brewer-michael/ns-cspgasp-rebuild/ref-images/IMG_2893.jpg

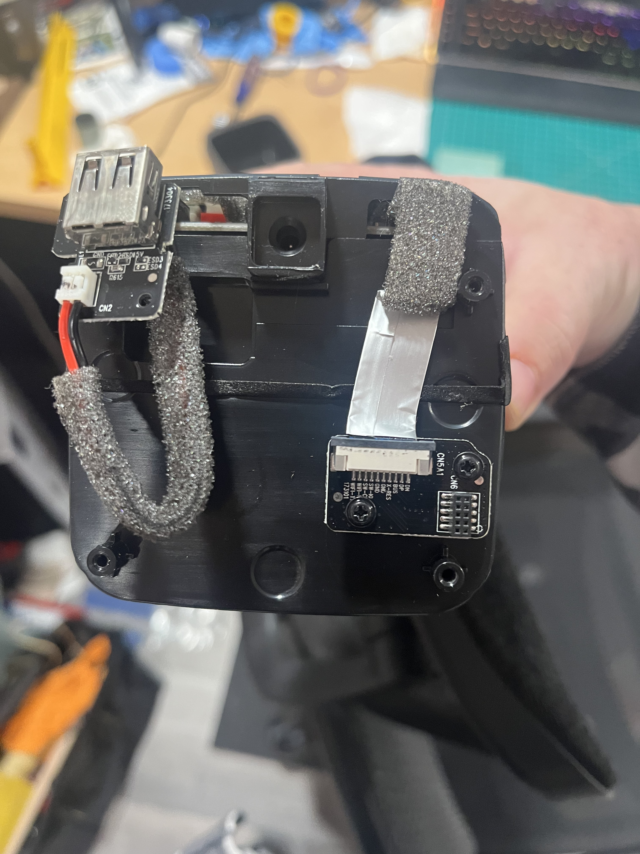
ref-images/IMG_2893.jpg
