brewer-michael/ns-cspgasp-rebuild/ref-images/IMG_2894.jpg

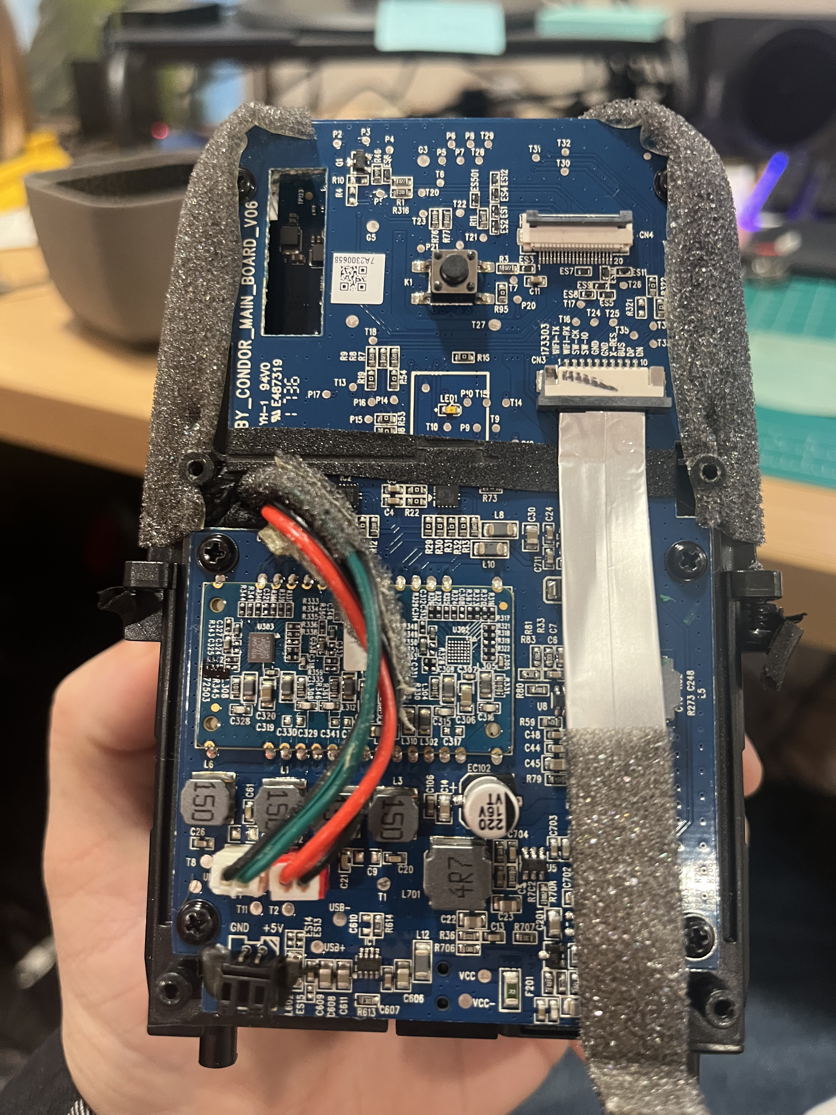
ref-images/IMG_2894.jpg
