brewer-michael/ns-cspgasp-rebuild/ref-images/IMG_2895.jpg

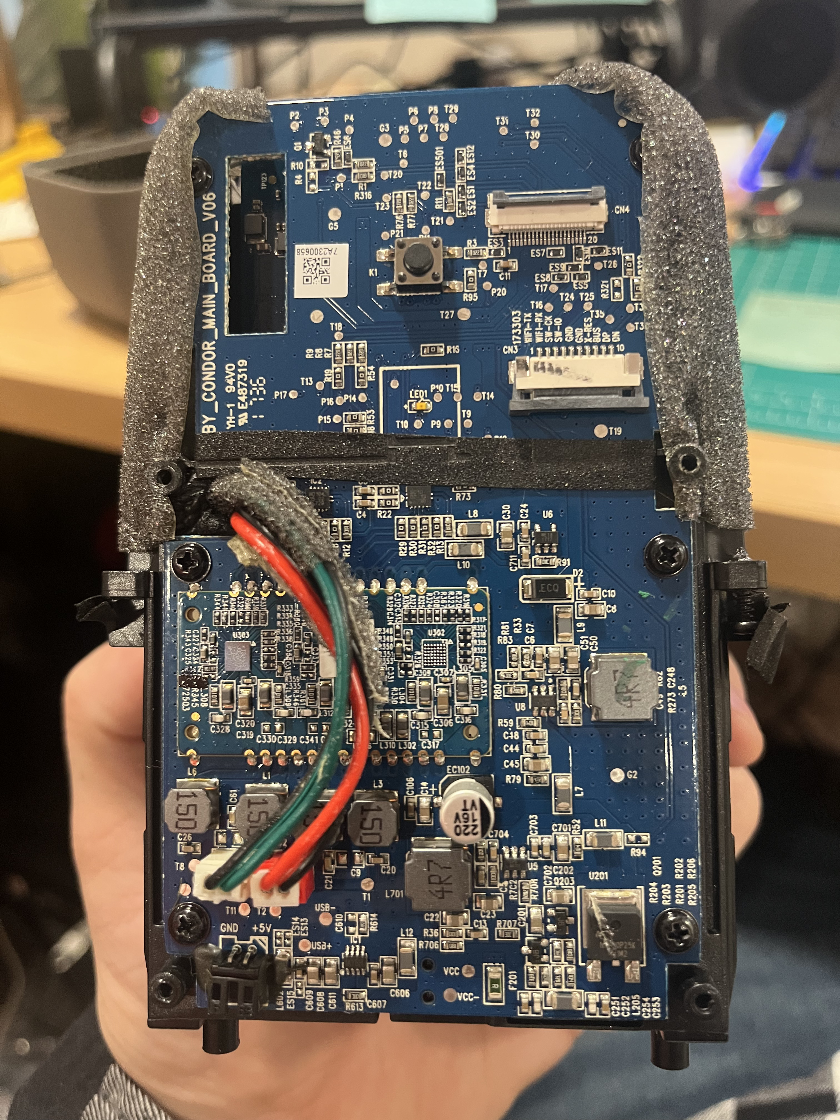
ref-images/IMG_2895.jpg
