brewer-michael/ns-cspgasp-rebuild/ref-images/IMG_2897.jpg

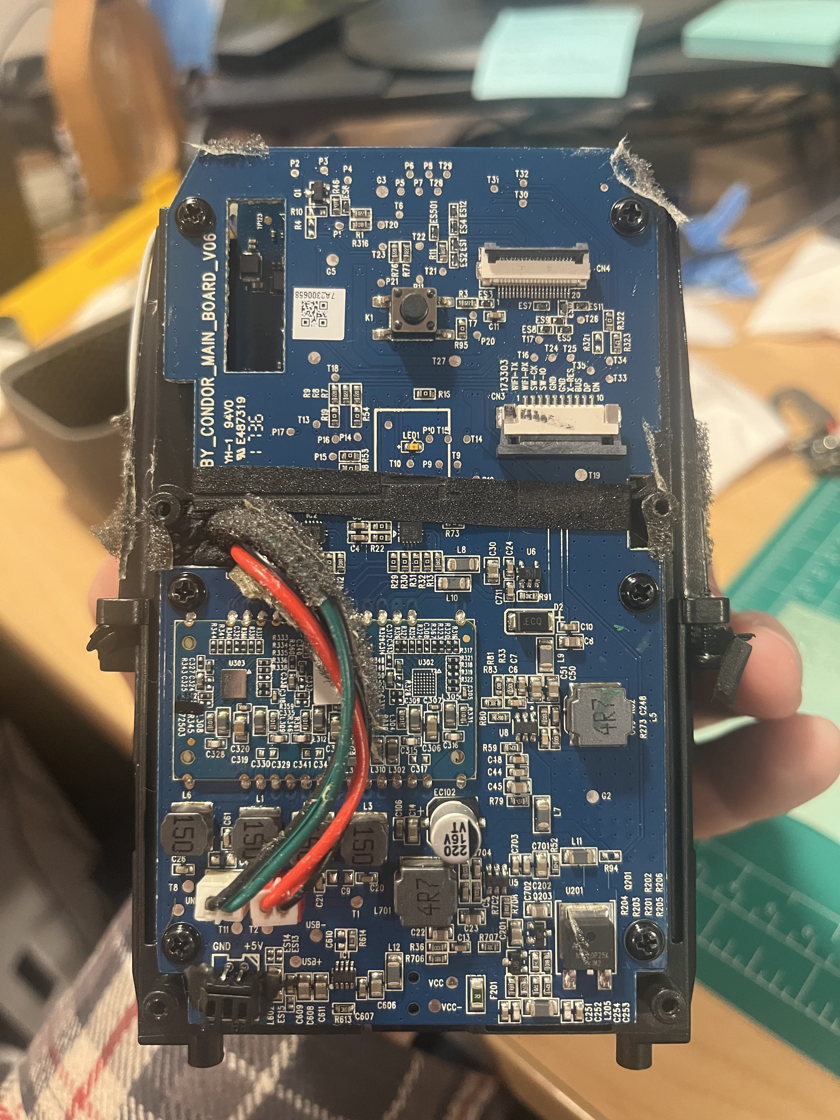
ref-images/IMG_2897.jpg
