brewer-michael/ns-cspgasp-rebuild/ref-images/IMG_2898.jpg

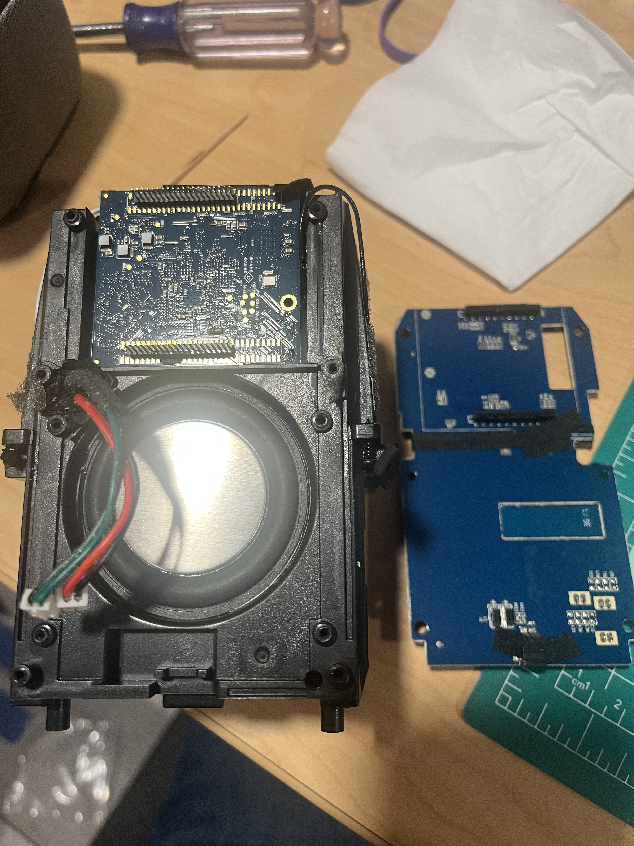
ref-images/IMG_2898.jpg
