brewer-michael/ns-cspgasp-rebuild/ref-images/IMG_2899.jpg

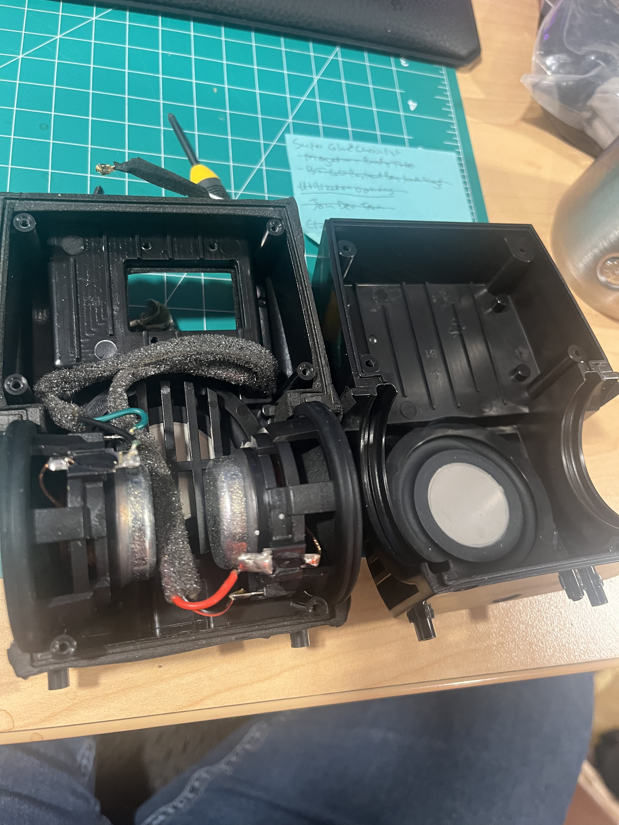
ref-images/IMG_2899.jpg
