brewer-michael/ns-cspgasp-rebuild/ref-images/IMG_2900.jpg

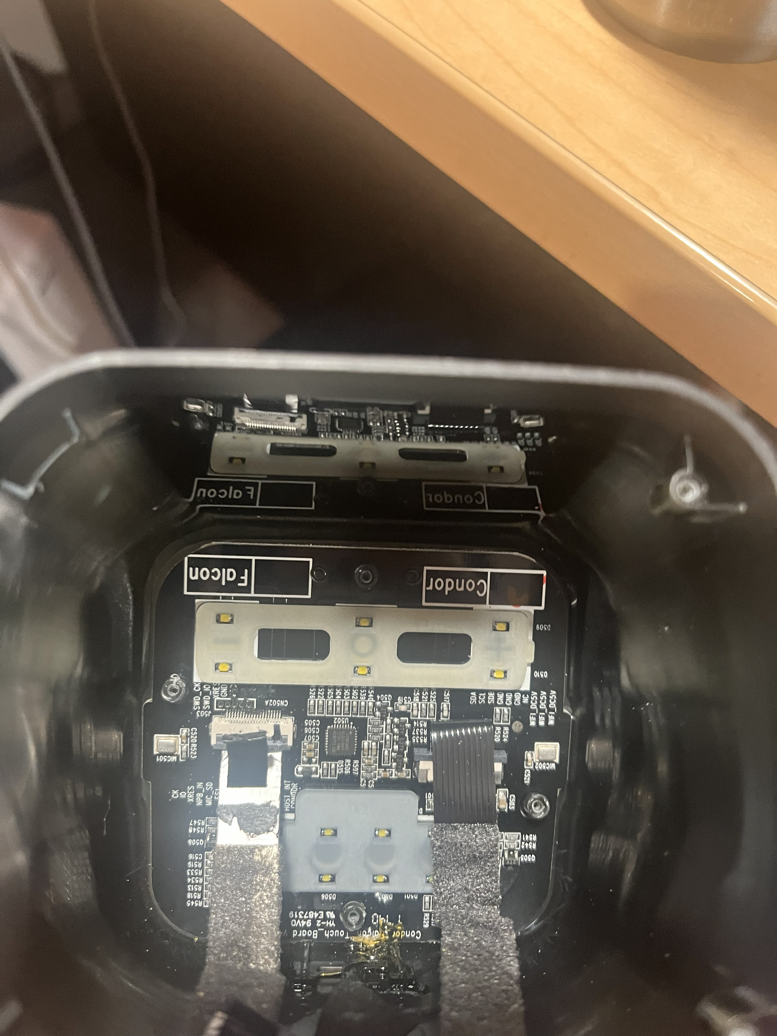
ref-images/IMG_2900.jpg
