brewer-michael/ns-cspgasp-rebuild/ref-images/IMG_2901.jpg

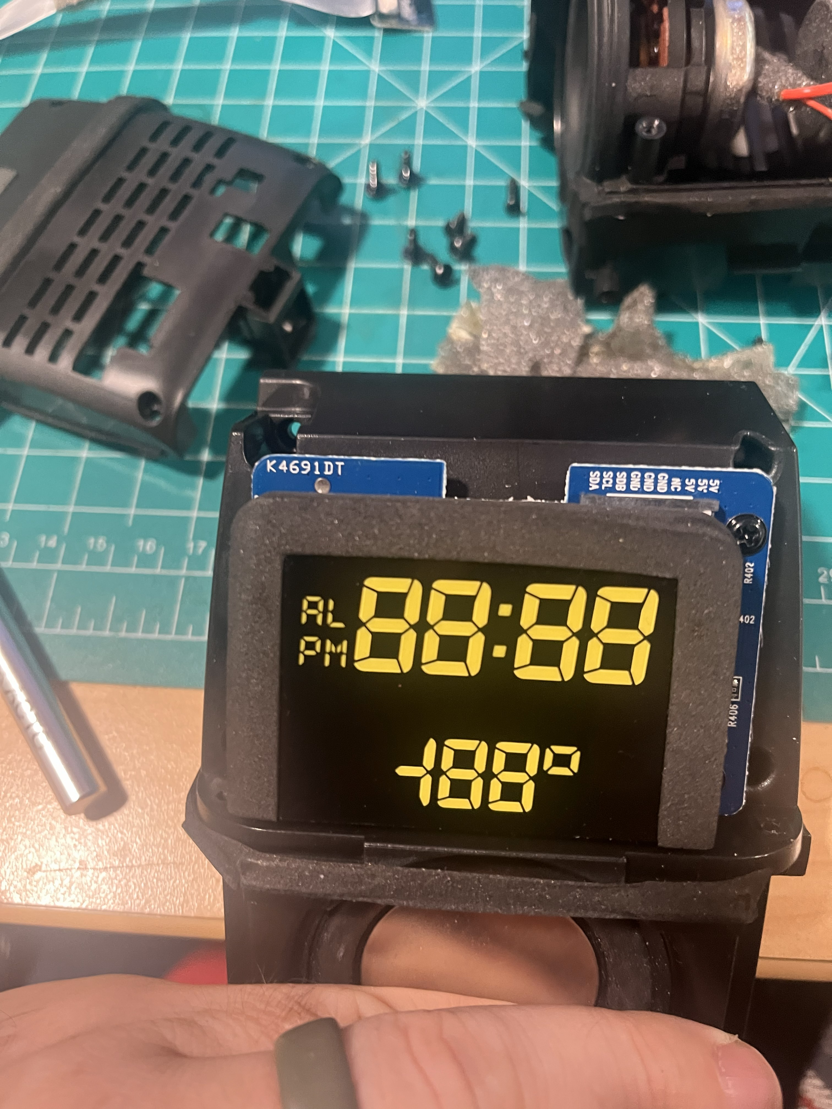
ref-images/IMG_2901.jpg
