brewer-michael/ns-cspgasp-rebuild/ref-images/IMG_2907.jpg

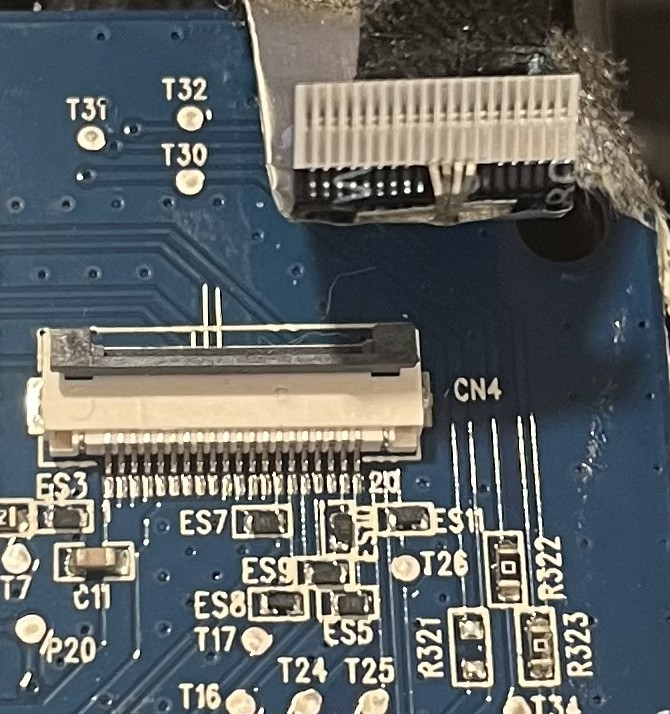
ref-images/IMG_2907.jpg
