brewer-michael/ns-cspgasp-rebuild/ref-images/IMG_2912.jpg

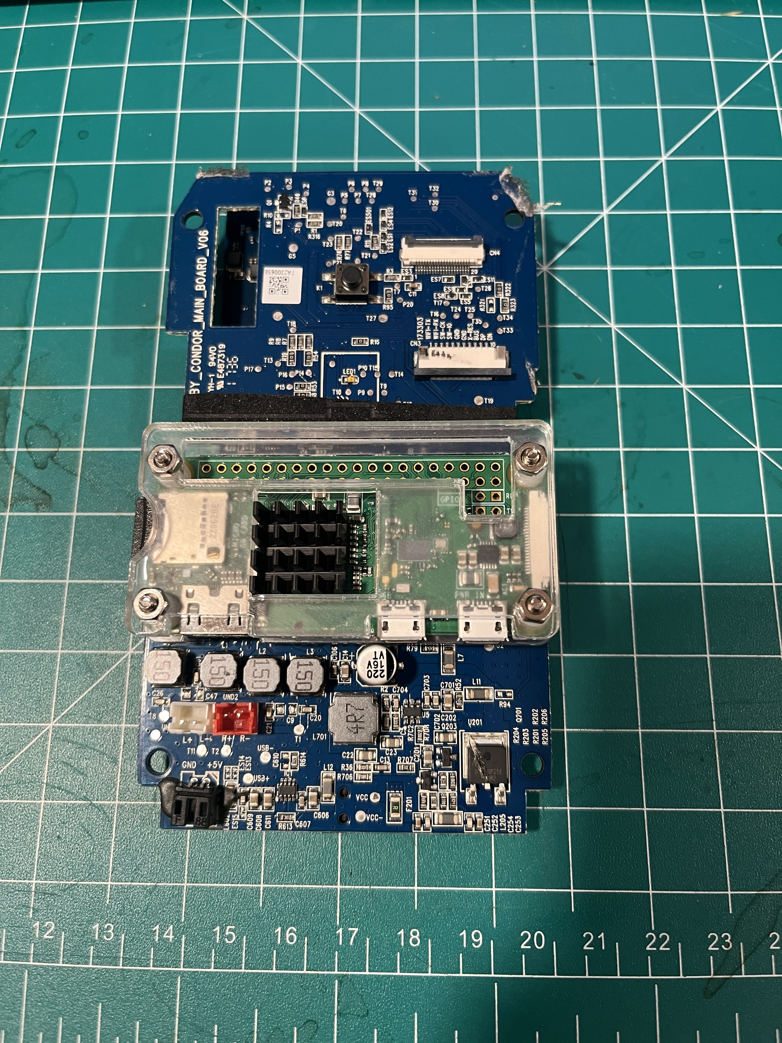
ref-images/IMG_2912.jpg
