brewer-michael/ns-cspgasp-rebuild/ref-images/IMG_2913.jpg

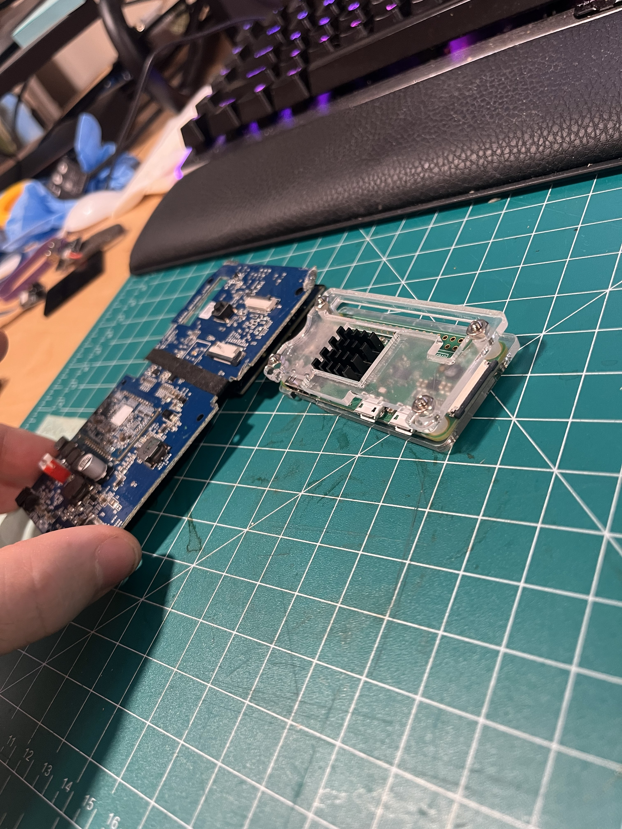
ref-images/IMG_2913.jpg
