brewer-michael/ns-cspgasp-rebuild/ref-images/IMG_2914.jpg

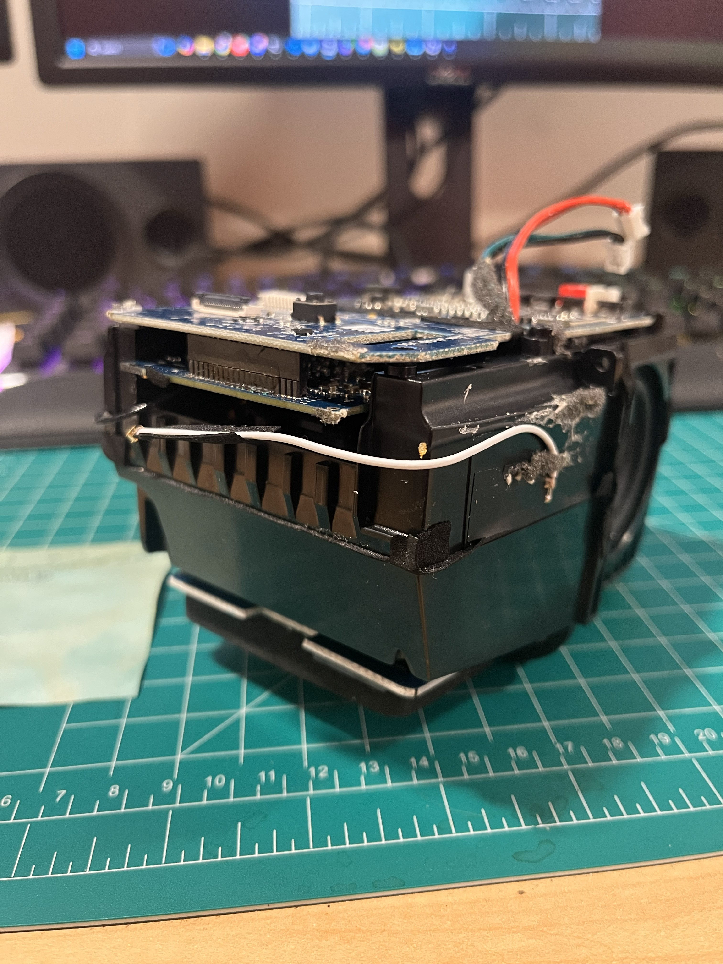
ref-images/IMG_2914.jpg
