brewer-michael/ns-cspgasp-rebuild/ref-images/IMG_2915.jpg

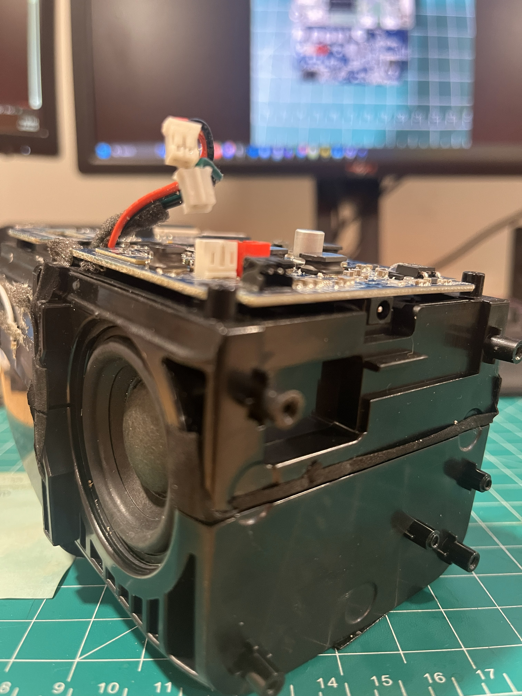
ref-images/IMG_2915.jpg
