brewer-michael/ns-cspgasp-rebuild/firmware/tests/test_factory.py

"""Building a Speaker and its components from the configuration."""

from __future__ import annotations

import asyncio
import contextlib
import socket
import sys
import types
from collections.abc import AsyncIterator, Callable, Iterator
from dataclasses import dataclass
from datetime import time as dtime

import aiohttp
import pytest
from conftest import make_config
from gpiozero import Device
from gpiozero.pins.mock import MockFactory, MockPWMPin

from open_speaker.agents import AgentChain
from open_speaker.agents.homeassistant import HomeAssistantAgent
from open_speaker.agents.openai_compat import OpenAiAgent
from open_speaker.app import Speaker
from open_speaker.audio.capture import Microphone
from open_speaker.audio.playback import AudioPlayer
from open_speaker.config import Config
from open_speaker.factory import build_speaker
from open_speaker.hardware.buttons import Buttons
from open_speaker.hardware.leds import SPI_HZ, StatusLeds
from open_speaker.hardware.oled import Oled
from open_speaker.hardware.tm1637 import TM1637
from open_speaker.hardware.volume_led import VolumeLed
from open_speaker.homeassistant import HomeAssistant
from open_speaker.pipeline.homeassistant import HomeAssistantPipeline
from open_speaker.pipeline.local import LocalPipeline
from open_speaker.stt.openai_compat import OpenAiStt
from open_speaker.stt.wyoming import WyomingStt
from open_speaker.timers import Scheduler
from open_speaker.tts.openai_compat import OpenAiTts
from open_speaker.tts.wyoming import WyomingTts
from open_speaker.ui import Display, OledRenderer, Tm1637Renderer
from open_speaker.wake.local import MicroWakeWordEngine, OpenWakeWordEngine
from open_speaker.wake.wyoming import WyomingWakeEngine


@dataclass
class Listener:
    """A port on 127.0.0.1 that counts connection attempts."""

    port: int = 0
    connections: int = 0

    @property
    def uri(self) -> str:
        return f"tcp://127.0.0.1:{self.port}"

    @property
    def url(self) -> str:
        return f"http://127.0.0.1:{self.port}"


@pytest.fixture
async def listener() -> AsyncIterator[Listener]:
    result = Listener()

    async def on_connect(reader: asyncio.StreamReader, writer: asyncio.StreamWriter) -> None:
        result.connections += 1
        writer.close()

    server = await asyncio.start_server(on_connect, "127.0.0.1", 0)
    result.port = server.sockets[0].getsockname()[1]
    try:
        yield result
    finally:
        server.close()
        await server.wait_closed()


@pytest.fixture
async def session() -> AsyncIterator[aiohttp.ClientSession]:
    async with aiohttp.ClientSession() as session:
        yield session


@pytest.fixture
async def build(session: aiohttp.ClientSession) -> AsyncIterator[Callable[[Config], Speaker]]:
    speakers: list[Speaker] = []

    def build(config: Config) -> Speaker:
        speaker = build_speaker(config, session)
        speakers.append(speaker)
        return speaker

    yield build
    for speaker in speakers:
        for coro in speaker.c.extra_tasks:
            coro.close()
        if speaker.c.display is not None:
            await speaker.c.display.stop()
        if speaker.c.leds is not None:
            await speaker.c.leds.stop()
        if speaker.c.volume_led is not None:
            speaker.c.volume_led.close()


@pytest.fixture
def mock_gpio(monkeypatch: pytest.MonkeyPatch) -> Iterator[MockFactory]:
    factory = MockFactory(pin_class=MockPWMPin)
    monkeypatch.setattr(Device, "pin_factory", factory)
    yield factory
    factory.close()


@pytest.fixture
def no_gpio(monkeypatch: pytest.MonkeyPatch) -> None:
    """No GPIO library can be loaded, as on a PC."""
    monkeypatch.setattr(Device, "pin_factory", None)
    monkeypatch.setenv("GPIOZERO_PIN_FACTORY", "unavailable")


def free_port() -> int:
    with socket.socket() as sock:
        sock.bind(("127.0.0.1", 0))
        return sock.getsockname()[1]


# ---------------------------------------------------------------------------
# Voice pipelines


async def test_homeassistant_mode(build, tmp_path, listener, session) -> None:
    config = make_config(
        tmp_path, homeassistant={"url": listener.url, "token": "secret", "pipeline": "01jkitchen"}
    )
    speaker = build(config)
    c = speaker.c
    assert speaker.config is config
    assert isinstance(c.mic, Microphone)
    assert c.mic.config is config.audio.input
    assert isinstance(c.player, AudioPlayer)
    assert c.player.config is config.audio.output
    assert isinstance(c.homeassistant, HomeAssistant)
    assert (c.homeassistant.url, c.homeassistant.token) == (listener.url, "secret")
    assert isinstance(c.pipeline, HomeAssistantPipeline)
    assert (c.pipeline.ha, c.pipeline.pipeline_id, c.pipeline.vad) == (
        c.homeassistant,
        "01jkitchen",
        config.vad,
    )
    assert isinstance(c.scheduler, Scheduler)
    assert (c.scheduler.state_file, c.scheduler.missed_grace) == (config.timers_state_file, 600)
    assert (speaker.mic, speaker.player, speaker.pipeline, speaker.scheduler) == (
        c.mic,
        c.player,
        c.pipeline,
        c.scheduler,
    )
    assert c.session is session
    # The no-hardware config: no wake word engine, display, LEDs or HTTP API.
    assert speaker.wake is None
    assert c.wake is None
    assert c.display is None
    assert c.leds is None
    assert c.volume_led is None
    assert c.extra_tasks == []
    await asyncio.sleep(0.05)
    assert listener.connections == 0


async def test_local_mode_with_wyoming_servers(build, tmp_path, listener) -> None:
    config = make_config(
        tmp_path,
        homeassistant={"url": listener.url},
        pipeline={"mode": "local"},
        stt={"engine": "wyoming", "uri": listener.uri, "language": "en"},
        tts={"engine": "wyoming", "uri": listener.uri, "voice": "en_US-lessac-medium"},
        agents=[
            {"engine": "homeassistant", "agent_id": "conversation.ollama"},
            {"engine": "openai", "url": f"{listener.url}/v1", "model": "llama3.2"},
        ],
        wake={"engine": "wyoming", "uri": listener.uri, "names": ["ok_nabu"]},
    )
    speaker = build(config)
    pipeline = speaker.pipeline
    assert isinstance(pipeline, LocalPipeline)
    assert isinstance(pipeline.stt, WyomingStt)
    assert pipeline.stt.uri == listener.uri
    assert pipeline.stt_language == "en"
    assert isinstance(pipeline.tts, WyomingTts)
    assert (pipeline.tts.uri, pipeline.tts.voice) == (listener.uri, "en_US-lessac-medium")
    assert isinstance(pipeline.agents, AgentChain)
    home, model = pipeline.agents.agents
    assert isinstance(home, HomeAssistantAgent)
    assert (home.homeassistant, home.agent_id) == (speaker.c.homeassistant, "conversation.ollama")
    assert isinstance(model, OpenAiAgent)
    assert (model.endpoint, model.model) == (f"{listener.url}/v1/chat/completions", "llama3.2")
    assert isinstance(speaker.wake, WyomingWakeEngine)
    assert (speaker.wake.uri, speaker.wake.names) == (listener.uri, ["ok_nabu"])
    await asyncio.sleep(0.05)
    assert listener.connections == 0


async def test_local_mode_with_openai_servers_and_no_home_assistant(
    build, tmp_path, listener, session
) -> None:
    url = f"{listener.url}/v1"
    config = make_config(
        tmp_path,
        homeassistant={"url": None, "token": None},
        pipeline={"mode": "local"},
        stt={"engine": "openai", "url": url, "model": "whisper-small"},
        tts={"engine": "openai", "url": url, "voice": "af_heart"},
        agents=[{"engine": "openai", "url": url, "model": "llama3.2", "api_key": "sk-local"}],
    )
    speaker = build(config)
    assert speaker.c.homeassistant is None
    pipeline = speaker.pipeline
    assert isinstance(pipeline, LocalPipeline)
    assert isinstance(pipeline.stt, OpenAiStt)
    assert (pipeline.stt.endpoint, pipeline.stt.model) == (
        f"{url}/audio/transcriptions",
        "whisper-small",
    )
    assert isinstance(pipeline.tts, OpenAiTts)
    assert (pipeline.tts.endpoint, pipeline.tts.voice) == (f"{url}/audio/speech", "af_heart")
    (agent,) = pipeline.agents.agents
    assert isinstance(agent, OpenAiAgent)
    assert (agent.api_key, agent.session) == ("sk-local", session)
    await asyncio.sleep(0.05)
    assert listener.connections == 0


@pytest.mark.parametrize(
    ("wake", "engine"),
    [
        ({"engine": "none"}, type(None)),
        ({"engine": "microwakeword", "model": "hey_jarvis"}, MicroWakeWordEngine),
        ({"engine": "openwakeword", "model": "hey_rhasspy"}, OpenWakeWordEngine),
        ({"engine": "wyoming", "uri": "tcp://127.0.0.1:10400"}, WyomingWakeEngine),
    ],
)
async def test_wake_word_engines(build, tmp_path, wake, engine) -> None:
    speaker = build(make_config(tmp_path, wake=wake))
    assert type(speaker.wake) is engine
    assert speaker.c.wake is speaker.wake


async def test_timers_can_be_turned_off(build, tmp_path) -> None:
    assert build(make_config(tmp_path, timers={"enabled": False})).scheduler is None
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
